atoomnetmarc/n-teller-xl-diy/firmware/include/Colors.h

/*

Copyright 2025 Marc Ketel
SPDX-License-Identifier: Apache-2.0

*/

#ifndef COLORS_H
#define COLORS_H

#include <NeoPixelBusLg.h>

#define COLOR_BLUE   RgbColor(20, 20, 255)
#define COLOR_YELLOW RgbColor(128, 255, 0)
#define COLOR_GREEN  RgbColor(30, 255, 0)
#define COLOR_RED    RgbColor(255, 0, 0)

#endif
